robertrico/dino-homebrew/docs/images/DINO_09_10_2026_1.jpeg

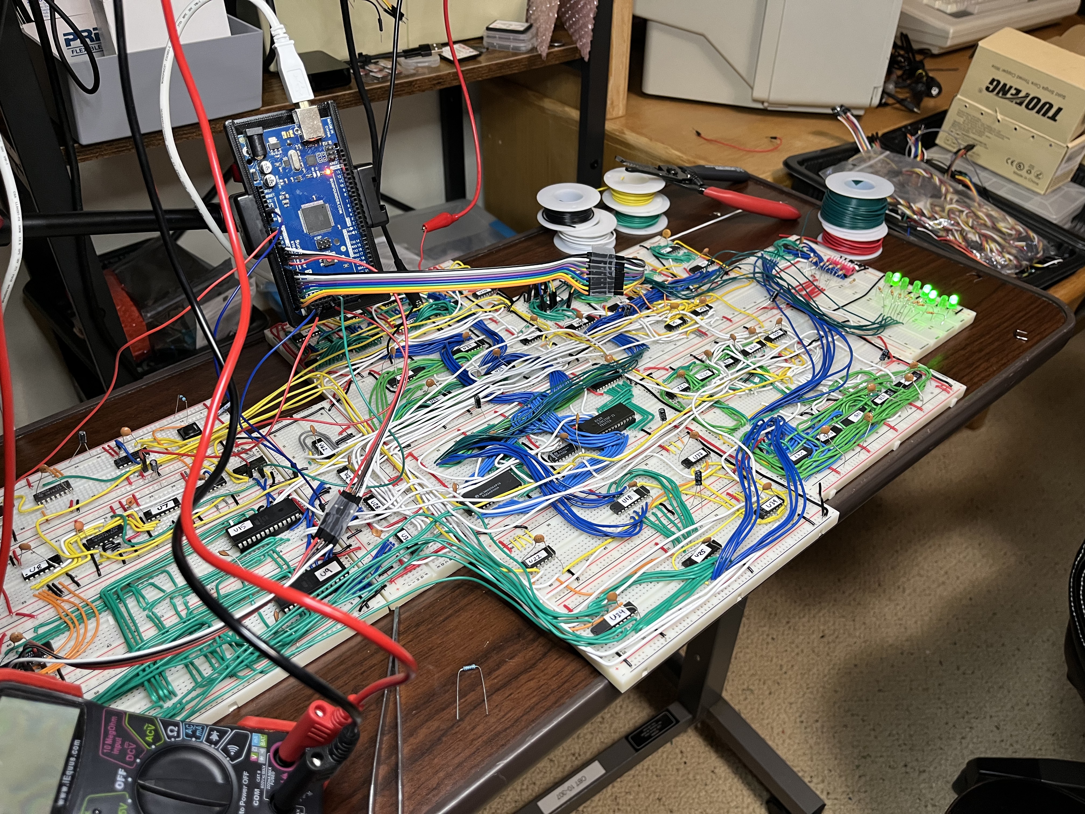
docs/images/DINO_09_10_2026_1.jpeg
