robertrico/dino-homebrew/asm/ram/bigxfer.asm

; bigxfer.asm -- the serial settle test. RAM-resident: loaded, not burned.
; 2026-09-29: RETURNS (5/5, retlda 40/40) with the T-state-0 write gate in copper
;   (U62 g4 + U56 3->4, .git/sdd/RAM_RET_FETCH.md). The results below are PRE-GATE.
;   load+run: make go-bigxfer        (asm/ram/bigxfer.asm -> RAM via L, then G)
;   soak:     python3 docs/notes/bigxfer_host.py --runs 5
;   check:    python3 docs/notes/test_bigxfer.py
;
; 2026-09-08, Rico: the fault is mechanical -- shifting the table changes
; it -- and 301 bytes loads consistently. Before the bench time goes to the
; PCB, one witness: a LARGE transfer, both directions, several times. This
; is it. About 2.2K goes IN through L (4400 characters, each echoed and
; checked, the sum witnessed by the monitor), then G runs it and it streams
; ITSELF back OUT: every byte from 0x8100 to its own end as two hex digits,
; 32 bytes a line, then one line
;
;     S hhll X xx
;
; with the 16-bit sum and the 8-bit xor of everything it read. The host
; compares the stream byte for byte against what it assembled, and the sums
; against its own. A wire that has settled passes this several times in a
; row; a wire that has not names the byte where it slipped.
;
; OB shows the pointer's HIGH byte while it streams, 0x81 up to 0x89: a
; stall names its page.
;
; The data is 2048 bytes from a seeded generator -- no structure, every
; value, so a stuck bit or a shifted nibble cannot hide. Code first, table
; after; the walk covers both, so the code bytes are read as data too.
;
; RAM: cells at 0x8000-0x800F. The monitor's 0x80E0-0x80FF is never touched.
; REGISTER DISCIPLINE, monitor.asm's rules: B is destroyed by every
; immediate-ALU op and by INR/DCR/SHL/NOT, so B is loaded right before each
; use; nothing lives in C across a CALL (RET's scratch).
; FIRST-OF-ITS-KIND: a RAM program reading its own code bytes as data
; through LDAX (life read only its tables); a 16-bit pointer walked across
; page boundaries 0x81..0x89 (every image so far kept its pointer in one
; page); JNC on ADD's carry to ripple a 16-bit sum (JNC has only ever
; followed SUB/CPI). Everything else is monitor idiom.
;
; 2026-10-06: the sum ripples with ACI 0 now, not JNC/INR -- NEEDS THE
; CARRY MICROCODE (U9 0x4102 U15 0x9BC4 U23 0x8A40). First RAM program on
; ACI; first ACI whose carry crossed LDA/STA rows to reach it.

PUTHEX:   .equ  0x02C4          ; monitor.asm, `make listing-monitor`
PUTC:     .equ  0x0345
CRLF:     .equ  0x036B

PTRL:     .equ  0x8000          ; walk pointer
PTRH:     .equ  0x8001
CUR:      .equ  0x8002          ; the byte just read
S16L:     .equ  0x8003          ; 16-bit sum
S16H:     .equ  0x8004
XR:       .equ  0x8005          ; 8-bit xor
COL:      .equ  0x8006          ; bytes on this line

          .org  0x8100

start:    MVI   PTRL, <start
          MVI   PTRH, >start
          CLR
          STA   S16L
          STA   S16H
          STA   XR
          STA   COL

loop:     LDB   PTRH
          LDC   PTRL
          LDAX                  ; A = [PTR]
          STA   CUR
          LDB   PTRH
          MOVAB
          OUT                   ; progress: the page on OB

          LDB   CUR             ; S16 += CUR, carry into the high byte
          LDA   S16L
          ADD
          STA   S16L
          LDA   S16H            ; LDA/STA hold the flags: ADD's carry
          ACI   0x00            ;   is still C here
          STA   S16H
          LDB   CUR             ; XR ^= CUR
          LDA   XR
          XOR
          STA   XR

          LDA   CUR             ; print it
          CALL  PUTHEX
          LDA   COL             ; 32 to a line
          INR
          STA   COL
          CPI   32
          JNZ   no_crlf
          CALL  CRLF
          CLR
          STA   COL
no_crlf:  LDA   PTRL            ; PTR += 1
          INR
          STA   PTRL
          JNZ   check
          LDA   PTRH
          INR
          STA   PTRH
check:    LDA   PTRL            ; until PTR == end
          CPI   <end
          JNZ   loop
          LDA   PTRH
          CPI   >end
          JNZ   loop

          LDA   COL             ; end the last line if it is open
          CPI   0
          JNZ   tail_crlf
          JMP   report
tail_crlf: CALL CRLF
report:   LDAI  'S'
          CALL  PUTC
          LDAI  ' '
          CALL  PUTC
          LDA   S16H
          CALL  PUTHEX
          LDA   S16L
          CALL  PUTHEX
          LDAI  ' '
          CALL  PUTC
          LDAI  'X'
          CALL  PUTC
          LDAI  ' '
          CALL  PUTC
          LDA   XR
          CALL  PUTHEX
          CALL  CRLF
          RET

; ---- the data: 2048 bytes, random.Random(0x0D1A0), regenerate with
; python3 -c "import random;r=random.Random(0x0D1A0);print(...)"
table:
          .db   0xC6, 0xA5, 0x89, 0x42, 0x63, 0x2E, 0x91, 0x6A, 0x98, 0xDD, 0x0A, 0x0E, 0xE5, 0x60, 0xDA, 0xA2
          .db   0x3F, 0xBA, 0xC1, 0xAE, 0xF3, 0xE6, 0xFC, 0x8C, 0xB1, 0xD5, 0x8F, 0x1A, 0x45, 0x46, 0x24, 0xA1
          .db   0x86, 0xBD, 0xBA, 0x51, 0xC6, 0x12, 0x52, 0x82, 0xD9, 0xED, 0x7C, 0x0A, 0x41, 0x05, 0x95, 0x2B
          .db   0xEB, 0xE7, 0xE5, 0x90, 0xF5, 0x7F, 0xE3, 0xA2, 0x23, 0xF5, 0x74, 0xDE, 0xF0, 0xC6, 0xCB, 0x08
          .db   0x19, 0xEB, 0xFE, 0x38, 0xCA, 0x19, 0x66, 0xC2, 0x02, 0xBE, 0xC4, 0x11, 0x0B, 0x94, 0xD9, 0xB2
          .db   0x2C, 0xF2, 0x97, 0xB5, 0x1C, 0xFF, 0xB0, 0x68, 0x16, 0x2F, 0x60, 0x61, 0x89, 0x59, 0xA7, 0x88
          .db   0xCE, 0xFB, 0x7B, 0xA7, 0xC5, 0x41, 0x51, 0xF1, 0x7D, 0x91, 0xAD, 0x83, 0x56, 0x4C, 0x8F, 0x3C
          .db   0xDF, 0xB4, 0x1A, 0x03, 0xC7, 0x4C, 0xCF, 0xF4, 0xBB, 0xA3, 0xEB, 0x55, 0xEE, 0xC8, 0x48, 0xB1
          .db   0x12, 0xB5, 0x9B, 0x51, 0x0B, 0xF9, 0x81, 0x4C, 0x28, 0xE8, 0x32, 0x85, 0x75, 0x05, 0x2A, 0xF0
          .db   0x5D, 0x03, 0x81, 0xD1, 0x6F, 0x68, 0xA7, 0xE8, 0x5D, 0x31, 0xB3, 0xF5, 0xEF, 0xC5, 0x6F, 0x8A
          .db   0x49, 0x15, 0x27, 0x9F, 0x3A, 0xCA, 0x32, 0x82, 0x6A, 0xDD, 0x6B, 0xCF, 0x0A, 0x72, 0x56, 0x4A
          .db   0xCE, 0x6F, 0x52, 0x78, 0xDD, 0x01, 0xA0, 0x11, 0xD0, 0x3B, 0xA5, 0x92, 0xD2, 0x59, 0xA6, 0x74
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
          .db   0xCD, 0xCD, 0xDB, 0x6A, 0xD6, 0x27, 0xED, 0x22, 0x6D, 0xD6, 0xBD, 0x80, 0x3E, 0x08, 0xC5, 0xFE
          .db   0x84, 0x0C, 0x22, 0xA4, 0x4E, 0xCB, 0x27, 0x4A, 0xBB, 0x31, 0x7B, 0x2E, 0x1E, 0x53, 0x30, 0x98
end:
