robertrico/dino-homebrew/docs/notes/microcode_gen.py

#!/usr/bin/env python3
"""DINO microcode ROM image generator.

Symbolic instruction table (dino_session_state.md "Instruction microwords")
-> U9.bin (word[7:0] = CW0-7) + U15.bin (word[15:8] = CW8-15), the diag
image pair, printed per-chip CRC16s, and the rig's expect header
(tests/dino_bringup/src/microcode_expect.h) so rig and ROM can never
disagree.

Address = {IR[7:0], T[3:0]} = opcode*16 + T. 4096 rows; A12 is grounded on
the board, so each 8K AT28C64B carries the image twice (mirrored halves).

Hard rules (session state, decision item 3 + HALT rule change 2026-07-14):
  - ALL 4096 rows programmed; unused rows = SAFE-FILL 0x1000 (END).
  - T0 of ALL 256 opcodes = universal fetch 0x600E.
  - HALT word = 0x8000, bit15 only, NO END bit.

Diag image (test spec "ROM images"): word = own 12-bit address in [11:0],
INVERTED top address nibble in [15:12] — catches stuck-high data lines.

Builder asserts implement the list in dino_design_notes.md ("Builder
assert list") — the POLICY layer of the four-layer defense.

Run: python3 microcode_gen.py            (writes roms/ + expect header)
Test: python3 test_microcode_gen.py
"""
import os, sys

HERE = os.path.dirname(os.path.abspath(__file__))
ROMS = os.path.normpath(os.path.join(HERE, "..", "..", "roms"))
HDR = os.path.normpath(os.path.join(
    HERE, "..", "..", "tests", "dino_bringup", "src", "microcode_expect.h"))

# ---- control word bit map (session state, v0.0.3, COMPLETE) ------------
HALT_BIT = 1 << 15          # raw tap, active high
MUX_PC = 1 << 14            # PC_MAR_MUX: PC=1, MAR=0
PC_UP = 1 << 13             # raw tap
END = 1 << 12               # raw tap

SA = {"CLR": 0b000, "BSUB": 0b001, "SUB": 0b010, "ADD": 0b011,
      "XOR": 0b100, "OR": 0b101, "AND": 0b110, "SET": 0b111}  # [11:9]

# U29's O5 and O7 were the last two free MISC codes; the stack spends both.
# O0 is the NONE slot and can never be reclaimed, so MISC IS NOW FULL -- the
# next code needs ~{MISC_BANK} wired plus a second '138, or step 1's I/O
# decode retiring REG_OUT_LOAD to free O6.
MISC = {"NONE": 0b000, "PC_CLEAR": 0b001, "PC_LOAD": 0b010, "COND": 0b011,
        "MDR_OUT": 0b100, "SP_UP": 0b101, "REG_OUT_LOAD": 0b110,
        "SP_DOWN": 0b111}                                     # [8:6] U29

# SRC/DST codes 0-7 are BANK 0 (U28/U30, unchanged since the ROMs were first
# burned). Codes 8-15 are BANK 1 (U70/U71), reached by driving the matching
# bank bit LOW. The low three bits are the SAME CW3-CW5 / CW0-CW2 the old
# decoder sees; only the enable moves. That is what makes widening additive:
# every burned row stays valid and nothing re-encodes.
SRC = {"NONE": 0b000, "ROM": 0b001, "RAM": 0b010, "REG_A": 0b011,
       "REG_B": 0b100, "REG_C": 0b101, "ALU": 0b110, "SW": 0b111,  # [5:3] U28
       # bank 1 (U70). Code 8 MUST be a real source, never a NONE slot:
       # SRC_ACTIVE is U28.O0 and floats HIGH whenever U28 is disabled, so
       # every bank-1 code already reads "a source is active" -- which is
       # what turns the U25 bridge on so the byte reaches W. A bank-1 NONE
       # would let MDR quietly supply W with nothing driving it.
       "SP_LO": 8, "SP_HI": 9, "PC_LO": 10, "PC_HI": 11,
       # INTERRUPTS, 2026-09-25 (PROPOSAL_INT C6). U70 O4/O5, pins 11/10,
       # NC until the INT hardware lands -- decoder-inert on today's copper.
       # KONST is the '244 holding K (the injected opcode, and both vector
       # bytes); FLAGS is the '245 putting FLAG_C/Z/V/N on MDR0-3, zeros
       # above. Both are bank 1, so both land on MDR, as the rule requires.
       "KONST": 12, "FLAGS": 13}

DST = {"NONE": 0b000, "REG_A": 0b001, "REG_B": 0b010, "REG_C": 0b011,
       "MAR_LO": 0b100, "MAR_HI": 0b101, "IR": 0b110, "RAM": 0b111,  # [2:0] U30
       # bank 1 (U71). These drive the '169s' ~PE, a SYNCHRONOUS load enable
       # -- which is why the stack needs no SP_LOAD misc code and why MISC
       # got away with the two slots it had left.
       "SP_LO": 8, "SP_HI": 9,
       # INTERRUPTS, 2026-09-25. U71 O2-O4, pins 13/12/11, NC today.
       # FLAGS drives the POPF '157 in front of U49 D0-3; IE_SET / IE_CLR
       # are the interrupt-enable flip-flop's set and clear.
       "FLAGS": 10, "IE_SET": 11, "IE_CLR": 12}

# ---- the third EEPROM, CW16-23 (U23) -----------------------------------
# Every bit is ACTIVE LOW so that 0xFF -- an erased AT28C64B -- is today's
# machine. Same reasoning that made HALT=0xFF: the safe state has to be the
# blank state, or an unburned ROM rants instead of idling.
CIN_SEL_N = 1 << 16     # 0 = ALU_CIN follows FLAG_C (ADC/SBB); 1 = opcode path
SRC_BANK_N = 1 << 17    # 0 = SRC bank 1 (U70); 1 = bank 0 (U28)
DST_BANK_N = 1 << 18    # 0 = DST bank 1 (U71); 1 = bank 0 (U30)
MISC_BANK_N = 1 << 19   # 0 = MISC bank 1; 1 = bank 0.  UNWIRED, in reserve
ADDR_SEL1_N = 1 << 20   # with CW14 as ADDR_SEL0.       UNWIRED, in reserve
FLAG_SEL0 = 1 << 21     # '153 4:1 select, bit 0  \  UNWIRED, in reserve
FLAG_SEL1 = 1 << 22     # '153 4:1 select, bit 1   >  sel 00=C 01=Z 10=V 11=N
FLAG_POL = 1 << 23      # '86 polarity           /   taken = flag XOR pol

# Every third-ROM bit set = the inert word. word() starts here and CLEARS
# bits, so a field nobody names is automatically safe.
INERT_THIRD = 0xFF << 16

FLAG_SEL = {"C": 0b00, "Z": 0b01, "V": 0b10, "N": 0b11}


class BuildError(Exception):
    """Raised by word()/check_word()/check_table(). Defined here rather than
    with the other policy code below because word() itself now refuses two
    encodings -- see the two numbered refusals in its cond branch."""


def _sa_bits(code):
    """Pack a '382 function code into CW9..CW11 BIT-REVERSED.

    The schematic labels CW9=SA2, CW10=SA1, CW11=SA0, and wires SA0 -> S0,
    SA1 -> S1, SA2 -> S2. So CW9 carries the '382's select MSB and CW11 its
    LSB. Packing the code LSB-first at CW9 therefore delivers it REVERSED:
    ADD (011) arrived as 110 = AND, which is precisely what the bench measured
    — 5 AND 3 = 1, 0x39 AND 0 = 0, 0 AND 0x39 = 0, three independent images
    all matching (2026-08-02).

    This survived every earlier test because reversing a field is INVISIBLE
    unless something computes with it: block1 checked ROM -> pin and found them
    self-consistent, and alu.ops drove SA from the rig, never using the
    microcode's encoding at all. test_microcode_gen.py now cross-checks this
    against the NETLIST so it cannot come back.
    """
    return ((code & 1) << 2) | (code & 2) | ((code >> 2) & 1)


def word(mux_pc=False, pc_up=False, end=False, halt=False,
         sa=None, misc="NONE", src="NONE", dst="NONE",
         cin_from_flag_c=False, cond=None):
    """One 24-bit control word.

    `src`/`dst` name a code in EITHER bank -- the bank bit is derived from
    the code, never passed by hand, so a caller cannot select `SP_LO` and
    forget to switch banks.

    `cond=(flag, pol)` encodes the '153/'86 branch glue: `flag` is one of
    C/Z/V/N and `pol` is 0 or 1, with `taken = flag XOR pol`. The hardware
    does not exist yet; the field is burned now so it never needs a reburn.
    """
    w = INERT_THIRD
    if halt: w |= HALT_BIT
    if mux_pc: w |= MUX_PC
    if pc_up: w |= PC_UP
    if end: w |= END
    if sa is not None: w |= _sa_bits(SA[sa]) << 9

    m, s, d = MISC[misc], SRC[src], DST[dst]
    w |= (m & 7) << 6
    w |= (s & 7) << 3
    w |= (d & 7)
    # Codes 8-15 live in bank 1, selected by driving the bank bit LOW.
    if s >= 8: w &= ~SRC_BANK_N
    if d >= 8: w &= ~DST_BANK_N
    if m >= 8: w &= ~MISC_BANK_N

    if cin_from_flag_c: w &= ~CIN_SEL_N
    if cond is not None:
        flag, pol = cond
        sel = FLAG_SEL[flag]
        # BOTH refusals below are for faults that ENCODE CLEANLY, BURN, and
        # then branch on the wrong thing with nothing to say so. Same class
        # as the bit-reversed SA field: invisible unless something computes.
        #
        # 1. U77 is a 2:1 on CW21 ALONE. CW22 is a no-connect. V (0b10) and
        #    N (0b11) both have bit 0 CLEAR, so encoding either drives CW21
        #    LOW and hands U62.3 FLAG_C. Refuse until CW22 is landed -- and
        #    when it is, DELETE this branch, do not weaken it.
        if sel & 2:
            raise BuildError(
                f"cond flag {flag!r} needs CW22, which is a NO-CONNECT: U77 "
                f"is a 2:1 on CW21 alone, so {flag} would select FLAG_C")
        # 2. word()'s contract says taken = flag XOR pol. The BUILT gate is
        #    COND_TAKEN = NOR(~{COND}, flag) = flag XOR 1, and there is no
        #    '86 anywhere in this machine. Encoder and copper agree at
        #    pol=1 only; pol=0 clears CW23 and inverts every branch the day
        #    polarity lands.
        if not pol:
            raise BuildError(
                "cond pol=0 needs FLAG_POL/CW23 and a '86; the built gate is "
                "COND_TAKEN = NOR(~{COND}, flag), which is pol=1")
        if not (sel & 1): w &= ~FLAG_SEL0
        if not (sel & 2): w &= ~FLAG_SEL1
        if not pol: w &= ~FLAG_POL
    return w


FETCH = word(mux_pc=True, pc_up=True, src="ROM", dst="IR")   # 0x600E
FILL = word(end=True)                                        # 0x1000, END

# A SETTLING STATE. No source, no destination, no strobe -- electrically
# identical to SAFE_FILL minus its END, and SAFE_FILL occupies 4000 rows of
# the image already, so this drives nothing new.
#
# WHY IT EXISTS, 2026-08-27. An instruction that loads an ALU operand and
# reads the ALU in the VERY NEXT state gives the '382 pair no settling time:
# the operand latch closes on the CLK edge that ends one state and the result
# must be valid inside the next. Every other instruction in the machine loads
# its operand in a PREVIOUS instruction and gets a whole fetch state for free.
#
# At 500kHz all 147 subtests of PROG_isa pass. At 1.024MHz the same image
# returns varying subtest numbers from identical resets. Subtract runs out of
# margin first, because a '382 complements B before the adder starts -- ADI
# passed in the same run that SUI failed.
#
# One state each, byte lengths unchanged, no package.
SETTLE = word()                                              # 0xFF0000


# ---- opcode assignments -------------------------------------------------
# PROPOSED TABLE (2026-07-16). Only LDAI=0x11 is documented (addressing
# example in dino_session_state.md) — everything else is a fresh assignment:
# high nibble = family (0=ctl, 1=imm loads, 2=memory, 3=flow, 4=ALU, 5=io),
# HALT=0xFF so an ERASED program EEPROM (all 0xFF) halts instead of raving.
# Renumbering = edit here, rerun, reburn; the rig follows via the header.
OPCODES = {
    "NOP": 0x00,
    "LDAI": 0x11, "LDBI": 0x12, "LDCI": 0x13,
    "LDA": 0x21, "STA": 0x22,
    "JMP": 0x31, "JNZ": 0x32,
    "ADD": 0x41, "SUB": 0x42, "AND": 0x43, "OR": 0x44,
    "XOR": 0x45, "CLR": 0x46, "SET": 0x47, "BSUB": 0x48,
    # 0x52 WAS `IN`, RETIRED 2026-08-27 (Rico), at the burn SECTION 5 named.
    # It went in two stages and they are different KINDS of retirement:
    # phase E retired it in COPPER (U28.7 unlanded, ~{SW_OUT} deleted, SW1
    # answers at an ADDRESS as card zero and LDA replaces it) but kept the
    # row, because phase E burned no microcode ROM and deleting a row would
    # have cost three ROMs for nothing. Phase F writes all three anyway.
    # Executing IN on today's copper reads an UNDEFINED byte, not the park:
    # src=SW asserts SRC_ACTIVE so U25 is enabled, but SW asserts neither
    # ~{ROM_OUT} nor ~{RAM_OUT}, so READS_IDLE stays high and U25 drives W
    # from a floating MDR. 0x52 is free. Nothing claims it.
    "OUT": 0x51,
    # --- the stack, 2026-08-10 ------------------------------------------
    # LXISP joins the immediate-load family; CALL/RET join flow; PUSH/POP
    # open a 0x6x stack family. All five are reachable only because the
    # third EEPROM widened SRC and DST.
    "LXISP": 0x14,
    "CALL": 0x33, "RET": 0x34,
    "PUSHA": 0x61, "POPA": 0x62, "PUSHB": 0x63, "POPB": 0x64,
    "HALT": 0xFF,

    # --- PHASE F, 2026-08-27: forty free instructions plus JNC ----------
    # SECTION 6 of .git/sdd/PHASE_F.md is the collision-free map and this is
    # it, verbatim. Family 9 (SHR/MOV A,FLAGS/ADC/SBB) is NOT here: those
    # need packages that are not in sockets, and family 9 means "does not
    # exist until a package lands".
    #
    # ONE BURN COVERS ALL OF THEM. A new opcode writes rows in every byte of
    # the 24-bit word, so three ROMs is the cost of adding one instruction
    # AND the cost of adding forty-one. Adding MOV A,C alone would have cost
    # exactly what this costs.
    "RST": 0x01,
    "LDB": 0x23, "LDC": 0x24, "STB": 0x25, "STC": 0x26,
    "LDAS": 0x27, "STAS": 0x28,
    "JMPX": 0x35, "JMPSP": 0x36,
    "JNC": 0x37,                    # the ONLY one that needs U77
    "CMP": 0x49, "CMPB": 0x4A, "TST": 0x4B,
    "SHL": 0x4C, "INR": 0x4D, "DCR": 0x4E, "NOT": 0x4F,
    "PUSHC": 0x65, "POPC": 0x66,
    "INXSP": 0x67, "DCXSP": 0x68, "SPHL": 0x69, "HLSP": 0x6A,
    "LDAX": 0x71, "STAX": 0x72, "LDBX": 0x73, "STBX": 0x74,
    "LDCX": 0x75, "STCX": 0x76,
    # MOV dst,src -- the mnemonic reads MOVAB = "MOV A,B" = A <- B. The
    # names carry no comma because they are dict keys and assembler steps.
    "MOVAB": 0x81, "MOVAC": 0x82, "MOVBA": 0x83,
    "MOVBC": 0x84, "MOVCA": 0x85, "MOVCB": 0x86,
    "MOVASPL": 0x87, "MOVASPH": 0x88, "MOVSPLA": 0x89, "MOVSPHA": 0x8A,
    "MOVAPCL": 0x8B, "MOVAPCH": 0x8C,
}

# operand-fetch prefix shared by every MAR-consuming instruction:
# T1 -> MAR_LO, T2 -> MAR_HI (both fetch a byte, PC++)
_MARFILL = [word(mux_pc=True, pc_up=True, src="ROM", dst="MAR_LO"),   # 0x600C
            word(mux_pc=True, pc_up=True, src="ROM", dst="MAR_HI")]   # 0x600D


def _alu(op):
    return [word(end=True, sa=op, src="ALU", dst="REG_A")]


# SP -> MAR, the two-state prefix every stack access starts with. SP is a
# number, not an address driver (Route B), so MAR does the pointing.
_SP_TO_MAR = [word(src="SP_LO", dst="MAR_LO"),
              word(src="SP_HI", dst="MAR_HI")]


# B:C -> MAR, the two-state prefix every indexed access starts with. C is
# the LOW half: MAR_LO is loaded first and from C, without exception. A
# swapped pair is an off-by-256 and a round trip through the same pointer
# cannot see it.
_BC_TO_MAR = [word(src="REG_C", dst="MAR_LO"),
              word(src="REG_B", dst="MAR_HI")]


def _PUSH_BYTE(src):
    """Store one byte at [SP], then decrement. Empty-descending."""
    return _SP_TO_MAR + [word(src=src, dst="RAM"), word(misc="SP_DOWN")]


def _PUSH(reg):
    states = _PUSH_BYTE(reg)
    return states[:-1] + [word(misc="SP_DOWN", end=True)]


def _POP(reg):
    """Increment first, THEN load -- the mirror of PUSH's store-then-drop."""
    return ([word(misc="SP_UP")] + _SP_TO_MAR
            + [word(end=True, src="RAM", dst=reg)])


# instruction -> (byte length, [T1, T2, ...]); T0 is implicit FETCH
INSTRUCTIONS = {
    "NOP": (1, [word(end=True)]),
    "LDAI": (2, [word(mux_pc=True, pc_up=True, end=True, src="ROM", dst="REG_A")]),
    "LDBI": (2, [word(mux_pc=True, pc_up=True, end=True, src="ROM", dst="REG_B")]),
    "LDCI": (2, [word(mux_pc=True, pc_up=True, end=True, src="ROM", dst="REG_C")]),
    "LDA": (3, _MARFILL + [word(end=True, src="RAM", dst="REG_A")]),
    "STA": (3, _MARFILL + [word(end=True, src="REG_A", dst="RAM")]),
    "JMP": (3, _MARFILL + [word(end=True, misc="PC_LOAD")]),
    # JNZ NAMES ITS FLAG NOW, and that is the CW22 cure, not cosmetics.
    # A bare misc="COND" leaves the third ROM's default word -- CW21=1,
    # CW22=1, CW23=1 -- and under FLAG_SEL {CW22,CW21} = 0b11 is `N`, not
    # `Z`. It behaved as Z only because FLAG_Z was hardwired to U62.3. Land a
    # 4:1 on {CW22,CW21} later without a reburn and EVERY JNZ IN THE MACHINE
    # BECOMES JNN. cond=("Z",1) drives CW22 low now, so the second mux stage
    # is itself inert when it lands. pol=1 because the built gate is
    # COND_TAKEN = NOR(~{COND}, flag) and there is no '86 in this machine.
    "JNZ": (3, _MARFILL + [word(end=True, misc="COND", cond=("Z", 1))]),
    "ADD": (1, _alu("ADD")), "SUB": (1, _alu("SUB")),
    "AND": (1, _alu("AND")), "OR": (1, _alu("OR")),
    "XOR": (1, _alu("XOR")), "CLR": (1, _alu("CLR")),
    "SET": (1, _alu("SET")), "BSUB": (1, _alu("BSUB")),
    "OUT": (1, [word(end=True, misc="REG_OUT_LOAD", src="REG_A")]),
    # IN's ROW IS GONE, 2026-08-27. See OPCODES above for why, and
    # test_microcode_gen.test_IN_is_retired_from_the_isa for the guard that
    # stops it coming back. SW1 is read with LDA now -- it is memory.

    # --- the stack ------------------------------------------------------
    #
    # CONVENTION: empty-descending. SP points at the next FREE slot, PUSH
    # stores then decrements, POP increments then loads. A '169 has no
    # clear, so SP is RANDOM at power-up and every program must run LXISP
    # before touching the stack -- "machine works, then randomly doesn't"
    # traced to an unset SP is a miserable afternoon.
    #
    # SP never reaches the address bus directly (Route B). It is just a
    # number; MAR is the thing that points, so every stack access copies
    # SP into MAR first. That costs two T-states per access and buys back
    # the structural guarantee that M has exactly one driver pair.

    # LXISP addr -- the initialiser every program needs first.
    "LXISP": (3, [word(mux_pc=True, pc_up=True, src="ROM", dst="SP_LO"),
                  word(mux_pc=True, pc_up=True, end=True,
                       src="ROM", dst="SP_HI")]),

    "PUSHA": (1, _PUSH("REG_A")), "PUSHB": (1, _PUSH("REG_B")),
    "POPA": (1, _POP("REG_A")), "POPB": (1, _POP("REG_B")),

    # CALL addr -- push the return address, THEN fetch the target.
    #
    # The order is forced: CALL needs two 16-bit values alive at once (the
    # return address and the target) and MAR is the only 16-bit holder, so
    # the push has to finish before MAR is reused to fetch the target.
    #
    # THE PRICE, and it is a real one: what gets pushed is the address of
    # CALL's OPERAND BYTES, not the instruction after them. RET therefore
    # ends with two bare PC_UPs to step over them. Written once here,
    # host-tested, cannot drift.
    "CALL": (3, _PUSH_BYTE("PC_HI") + _PUSH_BYTE("PC_LO") + [
        word(mux_pc=True, pc_up=True, src="ROM", dst="MAR_LO"),
        word(mux_pc=True, pc_up=True, src="ROM", dst="MAR_HI"),
        word(end=True, misc="PC_LOAD"),
    ]),

    # RET -- pop two bytes back into MAR, load the PC from it, then step
    # over the operand bytes per the CALL convention above.
    #
    # The LO byte has to be parked somewhere while MAR is re-pointed at the
    # HI byte's slot, and C is the machine's only free register. That is
    # the whole reason RET clobbers C, and it is why C stays unavailable to
    # user code until a real scratch exists.
    "RET": (1, [
        word(misc="SP_UP"),
        word(src="SP_LO", dst="MAR_LO"),
        word(src="SP_HI", dst="MAR_HI"),
        word(src="RAM", dst="REG_C"),        # return LO parked in C
        word(misc="SP_UP"),
        word(src="SP_LO", dst="MAR_LO"),
        word(src="SP_HI", dst="MAR_HI"),
        # Return HI onto the bus with NO destination -- MDR shadows every W
        # transfer for free (U22 gate2: ~{MDR_EN} = NOR(SRC_ACTIVE, MDR_OUT),
        # so the U25 bridge is on whenever ANY source drives), and LE_MDR =
        # NAND(~{RAM_LOAD}, READS_IDLE) latches that byte the moment the read
        # ends. That gives RET the SECOND scratch it needs without a second
        # register, and it is why src=RAM dst=MAR_HI is NOT used here -- see
        # check_word's RAM-writes-MAR rule.
        word(src="RAM"),
        # REPLAY IMMEDIATELY -- the very next state, before anything else
        # drives MDR. U18's LE_MDR falls as ~{RAM_OUT} deasserts at the
        # T-state boundary, and if another source is turning ON across that
        # same boundary the latch can capture THAT byte instead. Found on the
        # gate model 2026-08-10: with one intervening REG_C -> MAR_LO state,
        # U18 latched C (0x0C) and RET loaded PC = 0x0C0C instead of 0x000C.
        # Reasoning said the park was safe; the model disagreed.
        word(misc="MDR_OUT", dst="MAR_HI"),  # parked HI out of MDR
        word(src="REG_C", dst="MAR_LO"),     # parked LO out of C
        word(misc="PC_LOAD"),                # PC <- M <- MAR
        word(pc_up=True),                    # step over operand byte 1
        word(pc_up=True, end=True),          # step over operand byte 2
    ]),

    "HALT": (1, [word(halt=True)]),

    # ====================================================================
    # PHASE F, 2026-08-27 -- forty instructions that cost no wire, plus JNC
    # which costs exactly one package (U77, the '157 flag mux).
    #
    # Every code below was ALREADY LANDED and, with five exceptions noted in
    # CLAUDE.md, already bench-proven. Nothing here decodes to a pin that has
    # never been driven; what was missing was rows, not copper.
    # ====================================================================

    # ---- JNC: the one instruction in this block that needs hardware -----
    # Identical to JNZ but for CW21. COND_TAKEN = NOR(~{COND}, flag), so the
    # machine has exactly ONE branch polarity -- "taken if the selected flag
    # is ZERO" -- and U77 changes which flag, never the sense.
    #
    # The '382 pair's CN+4 is a NOT-borrow on the subtract codes, so
    # FLAG_C = 0 means A < B unsigned. JNC is therefore an unsigned magnitude
    # branch, and with CMP it asks "less than" without destroying A. The free
    # polarity is also the RIGHT one for multi-byte arithmetic: ADD; JNC
    # skip; <carry into the high byte> is the carry-propagate idiom exactly.
    # That is luck, not design, and it is why FLAG_POL can stay unlanded.
    "JNC": (3, _MARFILL + [word(end=True, misc="COND", cond=("C", 1))]),

    # ---- register moves -------------------------------------------------
    # SRC 3/4/5 = U28.O3/O4/O5, DST 1/2/3 = U30.O1/O2/O3. U28.O5 and U30.O3
    # were first driven by RET (T10 and T4) on 2026-08-24; the rest have run
    # since the machine booted.
    #
    # MOV A,C is the row that RETIRES THE LDCI GAP. LDCI and NOP are the only
    # two instructions that have never executed, and LDCI is unreachable BY
    # DESIGN because C is RET's return-address scratch and nothing can read
    # it back. One row closes it. That gap was always MICROCODE-SOFT.
    "MOVAB": (1, [word(end=True, src="REG_B", dst="REG_A")]),
    "MOVAC": (1, [word(end=True, src="REG_C", dst="REG_A")]),
    "MOVBA": (1, [word(end=True, src="REG_A", dst="REG_B")]),
    "MOVBC": (1, [word(end=True, src="REG_C", dst="REG_B")]),
    "MOVCA": (1, [word(end=True, src="REG_A", dst="REG_C")]),
    "MOVCB": (1, [word(end=True, src="REG_B", dst="REG_C")]),

    # ---- SP and PC readback ---------------------------------------------
    # SRC 8/9 = U70.O0/O1 (bench-proven by PROG_sp), SRC 10/11 = U70.O2/O3
    # (bench-proven by CALL T3/T7), DST 8/9 = U71.O0/O1 (bench-proven by
    # LXISP). Registers sit on MDR0-7 and so does the SP readback pair, so
    # these are plain one-row transfers with no new decoder output.
    #
    # MOV A,SPL / MOV SPL,A are what make SP usable as a SECOND INDEX
    # REGISTER in a leaf routine: it can be saved and restored. A routine
    # that also uses CALL or PUSH cannot do this, and that is a real
    # constraint, not a footnote.
    "MOVASPL": (1, [word(end=True, src="SP_LO", dst="REG_A")]),
    "MOVASPH": (1, [word(end=True, src="SP_HI", dst="REG_A")]),
    "MOVSPLA": (1, [word(end=True, src="REG_A", dst="SP_LO")]),
    "MOVSPHA": (1, [word(end=True, src="REG_A", dst="SP_HI")]),
    "MOVAPCL": (1, [word(end=True, src="PC_LO", dst="REG_A")]),
    "MOVAPCH": (1, [word(end=True, src="PC_HI", dst="REG_A")]),

    # B:C <-> SP, the union of the two rows above. C is the LOW half
    # throughout this document and this file -- see the pointer group.
    "SPHL": (1, [word(src="REG_C", dst="SP_LO"),
                 word(end=True, src="REG_B", dst="SP_HI")]),
    "HLSP": (1, [word(src="SP_LO", dst="REG_C"),
                 word(end=True, src="SP_HI", dst="REG_B")]),

    # ---- compares: an ALU op with NO destination -------------------------
    # U49 (the '273 flag latch) HAS NO CLOCK ENABLE -- it re-clocks every
    # T-state -- and U48's select is ~{ALU_OUT}. So the flags update on any
    # row that sources the ALU, whether or not anything latches the result.
    # DST 0 is U30.O0, the NONE slot, a no-connect by design.
    #
    # CMP is what makes JNC worth having: SUB then JNZ can only ask "equal or
    # not", and CMP + JNC asks "less than" without destroying A.
    "CMP": (1, [word(end=True, sa="SUB", src="ALU", dst="NONE")]),
    "CMPB": (1, [word(end=True, sa="BSUB", src="ALU", dst="NONE")]),
    "TST": (1, [word(end=True, sa="OR", src="ALU", dst="NONE")]),

    # ---- control ---------------------------------------------------------
    # MISC 1 = U29.O1, in use since the machine booted. RST is PC_CLEAR with
    # no operand: a one-byte software reset that does NOT clear the stack,
    # the registers or OB. Say which reset you mean.
    "RST": (1, [word(end=True, misc="PC_CLEAR")]),

    # MISC 5/7 = U29.O5/O7, bench-proven by POP and PUSH. SP_UP/SP_DOWN are
    # THE ONLY 16-BIT ARITHMETIC IN THE MACHINE and they touch neither the
    # ALU nor the flags. B:C has nothing comparable -- there is no carry path
    # between the registers -- so INXSP is the incrementer a monitor walks a
    # pointer with.
    "INXSP": (1, [word(end=True, misc="SP_UP")]),
    "DCXSP": (1, [word(end=True, misc="SP_DOWN")]),

    # ---- indirect jumps --------------------------------------------------
    # MISC 2 = U29.O2, in use by JMP. One byte: the target is in B:C or SP,
    # not in the instruction stream, so there is no PC_UP past the fetch.
    "JMPX": (1, [word(src="REG_C", dst="MAR_LO"),
                 word(src="REG_B", dst="MAR_HI"),
                 word(end=True, misc="PC_LOAD")]),
    "JMPSP": (1, _SP_TO_MAR + [word(end=True, misc="PC_LOAD")]),

    # ---- B:C as an index pair -------------------------------------------
    # C IS THE LOW BYTE. MAR_LO is loaded first and from C, everywhere in
    # this file, and a swapped pair is an off-by-256 that a round trip
    # through the SAME pointer cannot see -- the PROG_sp1 lesson, which
    # reported a green machine for most of 2026-08-24 with every bank-1
    # decoder output dead. Any witness for these must read back a cell only
    # a MOVED pointer reaches, by a path that cannot inherit the fault.
    #
    # src=RAM writing MAR is the forbidden case (the address feeds back into
    # the read while the '373 is transparent); this is not it -- MAR is
    # loaded from W, off the registers, before RAM is touched at all.
    "LDAX": (1, _BC_TO_MAR + [word(end=True, src="RAM", dst="REG_A")]),
    "LDBX": (1, _BC_TO_MAR + [word(end=True, src="RAM", dst="REG_B")]),
    "LDCX": (1, _BC_TO_MAR + [word(end=True, src="RAM", dst="REG_C")]),
    "STAX": (1, _BC_TO_MAR + [word(end=True, src="REG_A", dst="RAM")]),
    "STBX": (1, _BC_TO_MAR + [word(end=True, src="REG_B", dst="RAM")]),
    "STCX": (1, _BC_TO_MAR + [word(end=True, src="REG_C", dst="RAM")]),

    # ---- SP as a pointer -------------------------------------------------
    # The prefix is PUSH's, verbatim. A routine using LDAS/STAS cannot also
    # be using the stack for calls -- named in the docs, not hidden here.
    "LDAS": (1, _SP_TO_MAR + [word(end=True, src="RAM", dst="REG_A")]),
    "STAS": (1, _SP_TO_MAR + [word(end=True, src="REG_A", dst="RAM")]),

    # ---- absolute loads/stores for B and C -------------------------------
    # _MARFILL is LDA's prefix verbatim. DST 7 = U30.O7, in use by STA.
    "LDB": (3, _MARFILL + [word(end=True, src="RAM", dst="REG_B")]),
    "LDC": (3, _MARFILL + [word(end=True, src="RAM", dst="REG_C")]),
    "STB": (3, _MARFILL + [word(end=True, src="REG_B", dst="RAM")]),
    "STC": (3, _MARFILL + [word(end=True, src="REG_C", dst="RAM")]),

    # ---- C joins the stack ----------------------------------------------
    # Identical shape to PUSHA/POPA, bench-proven by PROG_sp2. Together with
    # MOV A,C these give C a life beyond being RET's scratch -- but RET still
    # clobbers it, so a routine that calls anything must not expect C to
    # survive the call.
    "PUSHC": (1, _PUSH("REG_C")), "POPC": (1, _POP("REG_C")),

    # ---- the TMP-shadow arithmetic ---------------------------------------
    # ALL FOUR CLOBBER B. That is the price and it is stated, not buried.
    #
    # They cost TWO rows and not four because U45/U46 (the ALU's TMP_A/TMP_B
    # '373 shadows) latch on the LOAD STROBE, not the opcode:
    #     LE_TMP_B = NOR(~{REG_B_LOAD}, CLK)          U50 g2
    # so ANY row with dst=REG_B fills TMP_B and the NEXT row's ALU op sees
    # it. Same mechanism that made the retired IN work in one microword.
    #
    # SHL:  row 1 copies A into B, so row 2 computes A + A.
    # INR:  SET makes 0xFF; A - 0xFF = A + 1 (mod 256).
    # DCR:  A + 0xFF = A - 1.
    # NOT:  A XOR 0xFF.
    # INR/DCR/NOT spend row 1 on the ALU itself (sa=SET, dst=REG_B), which
    # is why their first row sources ALU where SHL's sources REG_A.
    "SHL": (1, [word(src="REG_A", dst="REG_B"), SETTLE,
                word(end=True, sa="ADD", src="ALU", dst="REG_A")]),
    "INR": (1, [word(sa="SET", src="ALU", dst="REG_B"), SETTLE,
                word(end=True, sa="SUB", src="ALU", dst="REG_A")]),
    "DCR": (1, [word(sa="SET", src="ALU", dst="REG_B"), SETTLE,
                word(end=True, sa="ADD", src="ALU", dst="REG_A")]),
    "NOT": (1, [word(sa="SET", src="ALU", dst="REG_B"), SETTLE,
                word(end=True, sa="XOR", src="ALU", dst="REG_A")]),
}


# ==========================================================================
# PHASE F+, 2026-08-27 (Rico: "max the ceiling with all legal hardware-less
# instructions"). 108 more instructions, ZERO packages, ZERO new decoder
# outputs. Every row below uses a SRC, DST and MISC code that is already
# landed in copper and, with the five exceptions CLAUDE.md names, already
# bench-proven.
#
# WHY THIS MANY EXIST AT ALL. The decoders were widened twice -- for the
# stack (bank 1, 2026-08-10) and for CALL/RET (U72/U73, phase C) -- and the
# ROWS to use the new codes were only ever written for the instructions that
# motivated the widening. Everything here was legal the day the copper
# landed and simply had no opcode.
#
# THE ENUMERATION WAS EXHAUSTIVE, NOT INSPIRED. 227 distinct legal row
# sequences exist over the landed codes; 55 were already the ISA, 172 were
# new. These are the 108 that survived curation -- see _CUT, which names
# every rejected family and why, because "we considered it and said no" is
# not recoverable from an absence.
#
# THE BINDING CONSTRAINT MOVED. It is no longer hardware, it is the 256-entry
# opcode map: all 172 would have left 18 free, and family 9 plus the CW22 and
# CW23 branch families already claim 10 of those.
#
# HIGH NIBBLE IS STILL THE FAMILY. That is what lets a byte be
# hand-disassembled at the bench, so new families take CONTIGUOUS blocks and
# spill into 0xA-0xE rather than filling whatever hole comes next. 0x9x stays
# RESERVED: family 9 means "this opcode does not exist until a package lands".
# ==========================================================================

_CUT = {
    "CLR/SET with dst=NONE":
        "computes a constant and discards it; the flags it would set are "
        "known without executing it",
    "immediate + CLR/SET":
        "CLR and SET read no operand, so the immediate byte is fetched and "
        "ignored -- CLR with a wasted byte, not an instruction",
    "SP_LO <-> SP_HI transfers":
        "no use case was named. Copying half a pointer onto its own other "
        "half is not an addressing mode",
    "PC halves -> SP halves":
        "PUSHPCL/PUSHPCH already put the PC somewhere useful and JMPSP is "
        "the reverse direction",
    "ALU result -> SP_LO/SP_HI":
        "16 opcodes for SP arithmetic that an ALU op plus MOVSPLA does in "
        "two instructions. Too rare to earn a family",
    "LD/ST of the SP halves THROUGH the SP":
        "degenerate -- the pointer loading itself from what it points at",
    "conditional branch to SP":
        "JNZ over a JMPSP is two instructions and the case is rare",
    "OUT of an ALU result through the indexed/SP prefixes":
        "OUTM/OUTMX/OUTMS already read memory to OB; an ALU result needs no "
        "address at all",
}

# name -> opcode. FROZEN AND EXPLICIT. Blocks are contiguous and each names
# its family; test_microcode_gen asserts no collision and that not one
# pre-existing opcode moved. Renumbering costs a reburn AND a reassemble of
# every program image, so this table is append-only in practice.
_OPCODES_F_PLUS = {
    # 0x1x  immediate loads -- one SP half at a time
    "LXIL": 0x15, "LXIH": 0x16,
    # 0x2x  memory: SP-relative for B and C (A got LDAS/STAS in phase F)
    "LDBS": 0x29, "STBS": 0x2A, "LDCS": 0x2B, "STCS": 0x2C,
    # 0x3x  flow: indirect branches, then the indirect loads and stores that
    #       share their five-byte operand shape
    "JZX": 0x38, "JCX": 0x39, "JMPM": 0x3A, "JZM": 0x3B, "JCM": 0x3C,
    "LDAM": 0x3D, "LDBM": 0x3E, "STAM": 0x3F,
    # 0x4x  ALU -- the last free slot in the family
    "BIT": 0x40,
    # 0x5x  I/O: OUT from any SOURCE. U44 is a '245 with its A side on
    #       MDR0-7 and ~CE = ~{REG_OUT_LOAD}, so OB latches whatever is on
    #       the bus when the strobe fires. src=REG_A was a microcode
    #       convention, never a wire.
    "OUTB": 0x52, "OUTC": 0x53, "OUTSPL": 0x54, "OUTSPH": 0x55,
    "OUTPCL": 0x56, "OUTPCH": 0x57, "OUTI": 0x58,
    "OUTM": 0x59, "OUTMX": 0x5A, "OUTMS": 0x5B,
    # 0x6x  stack: push and pop the pointers themselves
    "PUSHPCH": 0x60, "PUSHSPL": 0x6B, "POPSPL": 0x6C,
    "PUSHSPH": 0x6D, "POPSPH": 0x6E, "PUSHPCL": 0x6F,
    # 0x7x  indexed through B:C
    "MVIX": 0x77, "STADDX": 0x78, "STSUBX": 0x79, "STBSUBX": 0x7A,
    "STANDX": 0x7B, "STORX": 0x7C, "STXORX": 0x7D,
    # 0x9x  RESERVED -- hardware-gated. 0x90-0x95 went to INTERRUPTS
    #       2026-09-25 (see _OPCODES_INT). SHR (U78), MOV A,FLAGS (U79),
    #       ADC/SBB (U80), and the CW22/CW23 branch families.
    # 0xAx  memory, overflow from 0x2x: save and restore the pointers, and
    #       store an immediate without going through A
    "LDSPL": 0xA0, "LDSPH": 0xA1, "STSPL": 0xA2, "STSPH": 0xA3,
    "STPCL": 0xA4, "STPCH": 0xA5, "MVI": 0xA6, "MVIS": 0xA7,
    #       I/O, overflow from 0x5x: OUT an ALU result without storing it
    "OUTADD": 0xA8, "OUTSUB": 0xA9, "OUTBSUB": 0xAA,
    "OUTAND": 0xAB, "OUTOR": 0xAC, "OUTXOR": 0xAD,
    # 0xBx  moves, overflow from 0x8x: B and C to and from the pointers
    "MOVBSPL": 0xB0, "MOVBSPH": 0xB1, "MOVCSPL": 0xB2, "MOVCSPH": 0xB3,
    "MOVSPLB": 0xB4, "MOVSPHB": 0xB5, "MOVSPLC": 0xB6, "MOVSPHC": 0xB7,
    "MOVBPCL": 0xB8, "MOVBPCH": 0xB9, "MOVCPCL": 0xBA, "MOVCPCH": 0xBB,
    # 0xC0-0xD2  ALU with an IMMEDIATE operand. The biggest real win here:
    #       LDBI n; ADD is 3 bytes and 2 instructions, ADI n is 2 and 1, and
    #       CPI n + JNC is compare-against-a-constant-and-branch in four
    #       bytes -- the shape every loop bound and every status poll wants.
    "ADI": 0xC0, "ADI_B": 0xC1, "ADI_C": 0xC2,
    "SUI": 0xC3, "SUI_B": 0xC4, "SUI_C": 0xC5,
    "BSUI": 0xC6, "BSUI_B": 0xC7, "BSUI_C": 0xC8,
    "ANI": 0xC9, "ANI_B": 0xCA, "ANI_C": 0xCB,
    "ORI": 0xCC, "ORI_B": 0xCD, "ORI_C": 0xCE,
    "XRI": 0xCF, "XRI_B": 0xD0, "XRI_C": 0xD1,
    "CPI": 0xD2,
    # 0xD3-0xDF  ALU result into B or C instead of A. Writing B makes B an
    #       accumulator, since dst=REG_B refills TMP_B through the shadow
    #       latch; writing C computes without destroying either operand,
    #       because C has no shadow.
    "ADD_B": 0xD3, "ADD_C": 0xD4, "SUB_B": 0xD5, "SUB_C": 0xD6,
    "BSUB_B": 0xD7, "BSUB_C": 0xD8, "AND_B": 0xD9, "AND_C": 0xDA,
    "OR_B": 0xDB, "OR_C": 0xDC, "XOR_B": 0xDD, "XOR_C": 0xDE,
    "CPX": 0xDF,
    # 0xEx  the ALU result straight to memory, absolute and SP-relative
    "STADD": 0xE0, "STSUB": 0xE1, "STBSUB": 0xE2,
    "STAND": 0xE3, "STOR": 0xE4, "STXOR": 0xE5,
    "STADDS": 0xE6, "STSUBS": 0xE7, "STBSUBS": 0xE8,
    "STANDS": 0xE9, "STORS": 0xEA, "STXORS": 0xEB,
}

# CLR and SET are excluded from every immediate and every compute-and-store
# family: neither reads an operand, so the byte would be fetched and thrown
# away. See _CUT.
_REAL_SA = ("ADD", "SUB", "BSUB", "AND", "OR", "XOR")

# The three MAR prefixes and the byte length each costs. Every memory-
# touching family below is one of these plus a final row, which is why
# adding an addressing mode to an operation is one line and not three.
_PREFIXES = {"":  (3, _MARFILL),      # absolute, two operand bytes
             "X": (1, _BC_TO_MAR),    # indexed through B:C
             "S": (1, _SP_TO_MAR)}    # SP-relative


def _f_plus():
    """Build the 108 from the field tables rather than typing them out.

    108 hand-written rows is 108 chances to transpose a code, and the SA bug
    proved that a field which agrees with itself but not with the wiring is
    invisible until something computes with it. Everything this returns goes
    through check_word and check_table like any other row.
    """
    I = {}
    # ---- ALU with an immediate. Row 1 IS LDBI's row without END, so the
    # operand lands in TMP_B through the shadow latch (LE_TMP_B =
    # NOR(~{REG_B_LOAD}, CLK) follows the LOAD STROBE, not the opcode) and
    # row 2 computes on it. Clobbers B, exactly as LDBI n; ADD already does.
    for op, sa in zip(("ADI", "SUI", "BSUI", "ANI", "ORI", "XRI"), _REAL_SA):
        for suffix, dst in (("", "REG_A"), ("_B", "REG_B"), ("_C", "REG_C")):
            I[op + suffix] = (2, [
                word(mux_pc=True, pc_up=True, src="ROM", dst="REG_B"),
                SETTLE,
                word(end=True, sa=sa, src="ALU", dst=dst)])
    I["CPI"] = (2, [word(mux_pc=True, pc_up=True, src="ROM", dst="REG_B"),
                    SETTLE,
                    word(end=True, sa="SUB", src="ALU", dst="NONE")])
    # ---- ALU result into B or C, and two more flag-only tests
    for op, sa in zip(("ADD", "SUB", "BSUB", "AND", "OR", "XOR"), _REAL_SA):
        for suffix, dst in (("_B", "REG_B"), ("_C", "REG_C")):
            I[op + suffix] = (1, [word(end=True, sa=sa, src="ALU", dst=dst)])
    I["BIT"] = (1, [word(end=True, sa="AND", src="ALU", dst="NONE")])
    I["CPX"] = (1, [word(end=True, sa="XOR", src="ALU", dst="NONE")])
    # ---- B and C to and from the pointer halves
    for r in ("B", "C"):
        for h in ("LO", "HI"):
            I[f"MOV{r}SP{h[0]}"] = (1, [word(end=True, src=f"SP_{h}",
                                             dst=f"REG_{r}")])
            I[f"MOVSP{h[0]}{r}"] = (1, [word(end=True, src=f"REG_{r}",
                                             dst=f"SP_{h}")])
            I[f"MOV{r}PC{h[0]}"] = (1, [word(end=True, src=f"PC_{h}",
                                             dst=f"REG_{r}")])
    # ---- OUT from any source
    for name, src in (("OUTB", "REG_B"), ("OUTC", "REG_C"),
                      ("OUTSPL", "SP_LO"), ("OUTSPH", "SP_HI"),
                      ("OUTPCL", "PC_LO"), ("OUTPCH", "PC_HI")):
        I[name] = (1, [word(end=True, misc="REG_OUT_LOAD", src=src)])
    I["OUTI"] = (2, [word(mux_pc=True, pc_up=True, end=True,
                          misc="REG_OUT_LOAD", src="ROM")])
    for name, sa in zip(("OUTADD", "OUTSUB", "OUTBSUB", "OUTAND", "OUTOR",
                         "OUTXOR"), _REAL_SA):
        I[name] = (1, [word(end=True, misc="REG_OUT_LOAD", sa=sa, src="ALU")])
    # ---- the three addressing modes, x the operations that lacked one
    for p, (nbytes, pre) in _PREFIXES.items():
        I["OUTM" + p] = (nbytes, list(pre) + [
            word(end=True, misc="REG_OUT_LOAD", src="RAM")])
        # STORE AN IMMEDIATE -- and it costs one more T-state than it looks
        # like it should, for a reason worth stating.
        #
        # There is ONE address bus. The immediate is fetched at the PC and
        # written at MAR, and CW14 cannot point M at both in the same state.
        # So: fetch with the mux on the PC and NO destination, which parks the
        # byte in MDR for free (LE_MDR follows every memory read), then replay
        # it out of MDR with the mux back on MAR.
        #
        # And a SETTLE between them, 2026-09-05, found on silicon by
        # PROG_test5. CW14 comes straight off the ROM and flips M to MAR
        # ~30ns before the source decode retires ~{ROM_OUT}; in that window
        # FETCH_RAM = NOR(~{ROM_OUT}, ~{RAM_EN}) fires, the RAM drives the
        # cell's OLD byte onto MDR, and U18 is still transparent (LE_MDR
        # closes on READS_IDLE, three gates after the decode). The park shut
        # on a fight: MVI 0x9E read back 0x90/0x9F. A src=NONE row with the
        # mux STILL on the PC lets READ drop with M in ROM, so nothing can
        # turn on and the latch closes on a bus U19 released. Only then does
        # M flip. PROG_isa never saw it: PLANT rewrites the same byte.
        #
        # AND THE PC STEPS IN THE SETTLE, NOT IN THE PARK. First cut of the
        # settle (2026-09-05, burned, U9 0xC52B / U15 0xAE3F) left pc_up on
        # the park row: PC stepped at the boundary, the ROM's address moved
        # at once, and ~150ns later the ROM was putting the NEXT byte on U19
        # while U18 was still transparent. test5 slots 2/3 read 0x00/0xFF.
        # A ROM park is only safe while the ROM's ADDRESS stays put, so the
        # park reads without stepping and the settle steps: the PC moves at
        # the END of the settle, after U18 has shut on the immediate.
        I["MVI" + p] = (nbytes + 1, list(pre) + [
            word(mux_pc=True, src="ROM"),
            word(mux_pc=True, pc_up=True),
            word(end=True, misc="MDR_OUT", dst="RAM")])
        for name, sa in zip(("STADD", "STSUB", "STBSUB", "STAND", "STOR",
                             "STXOR"), _REAL_SA):
            I[name + p] = (nbytes, list(pre) + [
                word(end=True, sa=sa, src="ALU", dst="RAM")])
    # ---- save and restore the pointers, absolutely
    for h in ("LO", "HI"):
        I[f"LDSP{h[0]}"] = (3, _MARFILL + [word(end=True, src="RAM",
                                                dst=f"SP_{h}")])
        I[f"STSP{h[0]}"] = (3, _MARFILL + [word(end=True, src=f"SP_{h}",
                                                dst="RAM")])
        I[f"STPC{h[0]}"] = (3, _MARFILL + [word(end=True, src=f"PC_{h}",
                                                dst="RAM")])
        I[f"LXI{h[0]}"] = (2, [word(mux_pc=True, pc_up=True, end=True,
                                    src="ROM", dst=f"SP_{h}")])
    # ---- SP-relative for B and C
    for r in ("B", "C"):
        I[f"LD{r}S"] = (1, _SP_TO_MAR + [word(end=True, src="RAM",
                                              dst=f"REG_{r}")])
        I[f"ST{r}S"] = (1, _SP_TO_MAR + [word(end=True, src=f"REG_{r}",
                                              dst="RAM")])
    # ---- conditional branch to B:C
    for name, flag in (("JZX", "Z"), ("JCX", "C")):
        I[name] = (1, _BC_TO_MAR + [word(end=True, misc="COND",
                                         cond=(flag, 1))])
    # ---- push and pop the pointers
    for h in ("LO", "HI"):
        I[f"PUSHSP{h[0]}"] = (1, _PUSH(f"SP_{h}"))
        I[f"POPSP{h[0]}"] = (1, _POP(f"SP_{h}"))
        I[f"PUSHPC{h[0]}"] = (1, _PUSH(f"PC_{h}"))
    # ---- MEMORY-INDIRECT, the third addressing mode. RET's shape,
    # generalised.
    #
    # src=RAM CANNOT write MAR -- the address feeds back into the read while
    # the '373 is transparent -- so the pointer's LO byte is parked in C, MAR
    # is re-pointed at the pointer's HI byte, that byte is parked in MDR and
    # REPLAYED IMMEDIATELY (MDR holds for exactly one state), and only then
    # is MAR complete.
    #
    # THE ASSEMBLER EMITS THE ADDRESS TWICE, as addr then addr+1. MAR loads
    # only from W and has no increment, so the pointer's second half must be
    # addressed explicitly. That is the price of the mode and why these cost
    # five bytes.
    #
    # Clobbers C. B SURVIVES -- which is what makes LDAM better than
    # LDC addr; LDB addr+1; LDAX: five bytes against seven, and one fewer
    # register destroyed.
    def _indirect(final):
        return (_MARFILL + [word(src="RAM", dst="REG_C")]
                + _MARFILL
                + [word(src="RAM"),
                   word(misc="MDR_OUT", dst="MAR_HI"),
                   word(src="REG_C", dst="MAR_LO")]
                + final)
    I["LDAM"] = (5, _indirect([word(end=True, src="RAM", dst="REG_A")]))
    I["LDBM"] = (5, _indirect([word(end=True, src="RAM", dst="REG_B")]))
    I["STAM"] = (5, _indirect([word(end=True, src="REG_A", dst="RAM")]))
    I["JMPM"] = (5, _indirect([word(end=True, misc="PC_LOAD")]))
    I["JZM"] = (5, _indirect([word(end=True, misc="COND", cond=("Z", 1))]))
    I["JCM"] = (5, _indirect([word(end=True, misc="COND", cond=("C", 1))]))
    return I


_F_PLUS = _f_plus()

# The two tables must name the SAME set. A row with no opcode is unreachable;
# an opcode with no row safe-fills to a silent END. Both are bugs a bare
# update() would hide.
if set(_F_PLUS) != set(_OPCODES_F_PLUS):
    raise BuildError(
        f"phase F+ tables disagree -- rows without opcodes: "
        f"{sorted(set(_F_PLUS) - set(_OPCODES_F_PLUS))}; opcodes without "
        f"rows: {sorted(set(_OPCODES_F_PLUS) - set(_F_PLUS))}")
_collide = set(_OPCODES_F_PLUS.values()) & set(OPCODES.values())
if _collide:
    raise BuildError(f"phase F+ opcode collision: "
                     f"{sorted(hex(o) for o in _collide)}")
OPCODES.update(_OPCODES_F_PLUS)
INSTRUCTIONS.update(_F_PLUS)


# ==========================================================================
# INTERRUPTS -- 2026-09-25, Rico. .git/sdd/PROPOSAL_INT.md, as ruled:
# all six in 0x9x, K = 0x90, vector K:K = 0x9090, PUSHF/POPF in.
#
# 8080-style injection. At an instruction boundary (END, or HALT) with IE
# set and ~{IRQ} pending, the hardware holds the ROM/RAM buffers off for
# the next T0, drives K onto MDR from a '244, and inhibits PC_UP. The FETCH
# row runs unchanged -- IR latches K -- so the opcode below is never read
# from memory, and the PC still holds the address of the instruction that
# was NOT fetched. Everything after T0 is ordinary microcode.
#
# Decoder-inert until the hardware lands: no row of any other opcode names
# KONST, FLAGS, IE_SET or IE_CLR (test_interrupts pins every old row).
# ==========================================================================
KONST = 0x90                    # the '244's strapping: opcode AND vector byte
INT_VECTOR = (KONST << 8) | KONST   # 0x9090, in RAM: the vector is SOFT --
                                    # whoever EIs plants JMP handler here

_OPCODES_INT = {"INT": KONST, "IRET": 0x91, "EI": 0x92, "DI": 0x93,
                "PUSHF": 0x94, "POPF": 0x95}

# INT's first push is CALL's, with IE_CLR riding on the SP_DOWN row, whose
# DST field is otherwise empty. The microcode clears IE, so the accept
# logic does not have to: IE is 0 six states before INT's END, which is the
# first boundary at which a second accept could happen.
_INT_PUSH_HI = _PUSH_BYTE("PC_HI")
_INT_PUSH_HI = _INT_PUSH_HI[:-1] + [word(misc="SP_DOWN", dst="IE_CLR")]

_INT = {
    # 11 rows, 12 T. No pc_up anywhere: the PC already points at the
    # unfetched instruction, because the injected T0 did not count.
    "INT": (1, _INT_PUSH_HI + _PUSH_BYTE("PC_LO") + [
        word(src="KONST", dst="MAR_LO"),
        word(src="KONST", dst="MAR_HI"),
        word(end=True, misc="PC_LOAD"),
    ]),

    # IRET is NOT "RET plus one row", which is what the proposal said.
    # RET parks the return address's LO byte in C, and C belongs to the
    # interrupted program -- an IRET built that way breaks R3 on every
    # interrupt that lands while C is live. IRET parks LO in the PC
    # instead: the PC is about to be overwritten, so it is the one 16-bit
    # holder in the machine that is free here. 13 rows, 14 T.
    "IRET": (1, [
        word(misc="SP_UP"),
        word(src="SP_LO", dst="MAR_LO"),
        word(src="SP_HI", dst="MAR_HI"),
        word(src="RAM"),                        # return LO parked in MDR
        word(misc="MDR_OUT", dst="MAR_LO"),     # replayed immediately
        word(misc="PC_LOAD"),                   # PC = {SP_HI, LO}: scratch
        word(misc="SP_UP"),
        word(src="SP_LO", dst="MAR_LO"),
        word(src="SP_HI", dst="MAR_HI"),
        word(src="RAM"),                        # return HI parked in MDR
        word(misc="MDR_OUT", dst="MAR_HI"),     # replayed immediately
        word(src="PC_LO", dst="MAR_LO"),        # LO back out of the PC
        # IE_SET rides on the load: re-enable and return are one state, so
        # no 8080-style "EI takes effect after the next instruction" rule
        # is needed. No trailing pc_up -- INT has no operand bytes.
        word(end=True, misc="PC_LOAD", dst="IE_SET"),
    ]),

    "EI": (1, [word(end=True, dst="IE_SET")]),
    "DI": (1, [word(end=True, dst="IE_CLR")]),

    "PUSHF": (1, _PUSH("FLAGS")),
    # U49 clocks on ~{CLK}, MID T-state, not at the end (P_POPF). The
    # first RAM row loads nothing and lets the byte settle onto W for a
    # whole state; the second loads FLAGS from it. One T-state, bought
    # instead of a timing argument on breadboard bus capacitance.
    "POPF": (1, [word(misc="SP_UP")] + _SP_TO_MAR + [
        word(src="RAM"),
        word(end=True, src="RAM", dst="FLAGS"),
    ]),
}

if set(_INT) != set(_OPCODES_INT):
    raise BuildError("interrupt tables disagree")
_collide = set(_OPCODES_INT.values()) & set(OPCODES.values())
if _collide:
    raise BuildError(f"interrupt opcode collision: "
                     f"{sorted(hex(o) for o in _collide)}")
OPCODES.update(_OPCODES_INT)
INSTRUCTIONS.update(_INT)

# ==========================================================================
# CARRY INTO THE ALU -- 2026-10-06, Rico. PHASE_F 3.3, built as U76 (a '157
# on the ALU board; PHASE_F called it U80 before the INT block took that
# number). S <- CW16, I0a <- FLAG_C, I1a <- NAND(SA1, SA0), Za -> U38.15.
#
# CN is a true carry on ADD and a not-borrow on SUB, so both want FLAG_C
# straight: ADC = A + B + C, SBB = A - B - (1 - C). The immediate forms are
# ADI/SUI with CW16 cleared on the ALU row only -- the operand fetch is
# src=ROM, and U48 holds the flags unless the ALU is the source, so the
# carry they read is the one the previous instruction left.
# ==========================================================================
_OPCODES_CARRY = {"ADC": 0x96, "SBB": 0x97, "ACI": 0x98, "SBI": 0x99}

_CARRY = {
    "ADC": (1, [word(end=True, sa="ADD", src="ALU", dst="REG_A",
                     cin_from_flag_c=True)]),
    "SBB": (1, [word(end=True, sa="SUB", src="ALU", dst="REG_A",
                     cin_from_flag_c=True)]),
    "ACI": (2, INSTRUCTIONS["ADI"][1][:-1] + [
        INSTRUCTIONS["ADI"][1][-1] & ~CIN_SEL_N]),
    "SBI": (2, INSTRUCTIONS["SUI"][1][:-1] + [
        INSTRUCTIONS["SUI"][1][-1] & ~CIN_SEL_N]),
}

if set(_CARRY) != set(_OPCODES_CARRY):
    raise BuildError("carry tables disagree")
_collide = set(_OPCODES_CARRY.values()) & set(OPCODES.values())
if _collide:
    raise BuildError(f"carry opcode collision: "
                     f"{sorted(hex(o) for o in _collide)}")
OPCODES.update(_OPCODES_CARRY)
INSTRUCTIONS.update(_CARRY)

# Assemblers refuse these by name. INT exists only as an injected opcode:
# fetched from memory, the FETCH row would count the PC and INT would push
# a return address one byte past the truth.
NOT_ASSEMBLABLE = frozenset({"INT"})


def _fields(w):
    """(misc, src, dst) as FULL codes, bank bits folded in.

    This MUST fold the bank bits, and the reason is concrete: bank-1 code 10
    (`PC_LO`) has low bits `010`, the same three bits `RAM` uses in bank 0.
    The bank-blind version of this function raised "src=RAM dst=RAM" on
    CALL's push row -- a false positive -- and would just as happily have
    MISSED a genuine bank-1 bus fight. Every rule below compares full codes.
    """
    misc = ((w >> 6) & 7) | (0 if w & MISC_BANK_N else 8)
    src = ((w >> 3) & 7) | (0 if w & SRC_BANK_N else 8)
    dst = (w & 7) | (0 if w & DST_BANK_N else 8)
    return misc, src, dst


def check_word(addr, w):
    """Per-word legality. addr names the row in errors."""
    misc, src, dst = _fields(w)
    where = f"row {addr:#05x} word {w:#06x}"
    # src device == dst device (RAM corrupts; register case is the warning)
    if src == SRC["RAM"] and dst == DST["RAM"]:
        raise BuildError(f"{where}: src=RAM dst=RAM")
    for r in ("REG_A", "REG_B", "REG_C"):
        if src == SRC[r] and dst == DST[r]:
            print(f"WARNING {where}: src=dst={r} (probable MOV typo)")
    # /MDR_OUT replay + ANY source, in EITHER BANK, = two MDR-bus drivers.
    # MISC is an independent field, so this is the one collision the
    # hardware cannot prevent: every SRC-driven buffer is gated by U28 or
    # U70, which are one-hot and mutually exclusive by construction, but
    # U18's ~{MDR_OUT} comes from U29 and can be asserted alongside any of
    # them. Bank 1 widened the set this has to cover from 7 sources to 11.
    if misc == MISC["MDR_OUT"] and src != SRC["NONE"]:
        raise BuildError(f"{where}: /MDR_OUT with src!=NONE (MDR-bus fight)")
    # A RAM READ CANNOT WRITE MAR IN THE SAME WORD. The RAM address IS MAR
    # (U54/U59 -> M), and MAR's '373s are TRANSPARENT while CLK is low -- so
    # src=RAM with dst=MAR_LO/MAR_HI closes a live combinational loop:
    # MAR -> M -> RAM -> MDR -> U25 -> W -> MAR. The address changes
    # underneath the read.
    #
    # Found the hard way on 2026-08-10: RET's first draft did exactly this to
    # get the return address's HI byte into MAR, and the gate model hung with
    # the PC at 0x8D00. Park the byte in MDR instead (src=RAM with NO dst --
    # MDR shadows it for free) and replay it with misc=MDR_OUT.
    #
    # ROM reads are NOT affected: their address comes from the PC through
    # MUX_PC, not from MAR, which is why _MARFILL's ROM->MAR_LO/MAR_HI rows
    # are safe and always have been.
    if src == SRC["RAM"] and dst in (DST["MAR_LO"], DST["MAR_HI"]):
        raise BuildError(f"{where}: src=RAM writing MAR (the address feeds "
                         f"back into the read while the '373 is transparent)")
    # SP cannot count and be read in the same word: the '169s commit on the
    # CLK edge that ENDS the T-state, so the byte on MDR during that state
    # is the PRE-count value while the row reads as though it were the
    # post-count one. Ambiguous by construction -- refuse to encode it.
    if misc in (MISC["SP_UP"], MISC["SP_DOWN"]) and src in (SRC["SP_LO"], SRC["SP_HI"]):
        raise BuildError(f"{where}: SP counted and read in the same word")
    # THE ADDRESS BUS CARRIES ONE ADDRESS. CW14 (PC_MAR_MUX) points M at the
    # PC or at MAR, and a row cannot have it both ways:
    #
    #   src=ROM  needs the PC on M    (mux_pc=1)
    #   src=RAM  needs MAR on M       (mux_pc=0)
    #   dst=RAM  needs MAR on M       (mux_pc=0)  -- the write address is MAR
    #
    # So src=ROM with dst=RAM is UNSATISFIABLE, and it does not fail loudly:
    # the mux stays on the PC and the byte is written to the PC's own address,
    # which is ROM, so the store simply evaporates.
    #
    # PAID FOR ON 2026-08-27. MVI/MVIX/MVIS were encoded exactly that way. On
    # the bench the symptom was a program whose answer CHANGED ON EVERY RESET
    # -- its loop counter was initialised with MVI, the store went nowhere,
    # and the count came from uninitialised RAM. Nothing in check_word looked
    # at CW14 at all, so 174 instructions passed the police with three of them
    # unable to work. The cure is the MDR park: fetch with the mux on the PC
    # and NO destination, then replay out of MDR with the mux on MAR.
    if src == SRC["ROM"] and dst == DST["RAM"]:
        raise BuildError(f"{where}: src=ROM with dst=RAM -- one address bus, "
                         f"and the fetch and the store want different halves "
                         f"of it. Park the byte in MDR and replay it")
    if (w & MUX_PC) and (src == SRC["RAM"] or dst == DST["RAM"]):
        raise BuildError(f"{where}: RAM accessed with mux_pc set -- M carries "
                         f"the PC, not MAR, so the access lands at the wrong "
                         f"address")
    if src == SRC["ROM"] and not (w & MUX_PC):
        raise BuildError(f"{where}: src=ROM without mux_pc -- M carries MAR, "
                         f"so the fetch reads the wrong address")
    # THE FLAG CARRY IS FOR ARITHMETIC ON THE ALU. CW16 low hands U38.15
    # FLAG_C through U76; the '382 ignores CN on its logic codes, and with
    # no ALU source nothing computes. Either row encodes cleanly, burns,
    # and silently does what the same row without the bit does.
    if not (w & CIN_SEL_N):
        sa_code = _sa_bits((w >> 9) & 7)
        if src != SRC["ALU"] or sa_code not in (SA["ADD"], SA["SUB"],
                                                SA["BSUB"]):
            raise BuildError(f"{where}: flag carry (CW16 low) needs src=ALU "
                             f"and ADD/SUB/BSUB -- CN means nothing else")
    # PC_UP + PC_LOAD same word: defined-but-fragile on '193 internals
    if (w & PC_UP) and misc == MISC["PC_LOAD"]:
        raise BuildError(f"{where}: PC_UP with /PC_LOAD")
    # IR changes only at fetch
    if dst == DST["IR"] and (addr & 0xF) != 0:
        raise BuildError(f"{where}: IR_LOAD outside T0")
    # T0 row of every opcode is the universal fetch
    if (addr & 0xF) == 0 and w != FETCH:
        raise BuildError(f"{where}: T0 row is not the fetch word {FETCH:#06x}")


def check_table(words):
    """Whole-image legality: per-word checks + per-opcode block shape."""
    assert len(words) == 4096
    for a, w in enumerate(words):
        check_word(a, w)
    for op in range(256):
        block = words[op * 16:op * 16 + 16]
        # an instruction must END (or HALT-freeze) before running off its
        # last defined state into safe-fill. Safe-fill is itself END, so
        # scan T1..last-non-fill row: that word must carry END or HALT.
        states = [w for w in block[1:] if w != FILL]
        if states and not (states[-1] & (END | HALT_BIT)):
            raise BuildError(f"opcode {op:#04x}: last state "
                             f"{states[-1]:#06x} has no END/HALT")
        _check_mar_before_ram(op, states)
        _check_mdr_replay_is_immediate(op, states)


def _check_mdr_replay_is_immediate(op, states):
    """misc=MDR_OUT must be the state IMMEDIATELY after the read that parked
    the byte.

    MDR is a genuinely useful second scratch -- U18 shadows every W transfer
    for free -- but the park is only good for ONE state. LE_MDR =
    NAND(~{RAM_LOAD}, READS_IDLE) falls as ~{RAM_OUT} deasserts at the
    T-state boundary, and if another source is turning ON across that same
    boundary the latch can capture THAT byte instead. It is a race, not a
    rule, so it cannot be reasoned about from the gate equations alone.

    Paid for on 2026-08-10: RET's second draft parked the return address's HI
    byte in MDR, moved the LO byte from C to MAR_LO, and only THEN replayed.
    U18 latched C, MAR_HI got 0x0C instead of 0x00, and RET loaded the PC
    with 0x0C0C. Every reading of the schematic said the park was safe; the
    gate model disagreed, which is the whole reason the FPGA is the primary
    instrument now.
    """
    for t, w in enumerate(states, start=1):
        misc, src, _ = _fields(w)
        if misc != MISC["MDR_OUT"]:
            continue
        if t < 2:
            raise BuildError(f"opcode {op:#04x} T{t}: MDR_OUT with no prior "
                             f"state to have parked a byte")
        prev_misc, prev_src, prev_dst = _fields(states[t - 2])
        # One src=NONE settle between the park and the replay is allowed,
        # and for a ROM-side park it is REQUIRED (see the MVI family): it
        # drives nothing and loads nothing, so the latch has nothing new to
        # capture, and it keeps the mux where the park left it so no
        # address-keyed enable can fire. 2026-09-05.
        if (prev_src == SRC["NONE"] and prev_dst == DST["NONE"]
                and prev_misc == MISC["NONE"] and t >= 3
                and (states[t - 2] & MUX_PC) == (states[t - 3] & MUX_PC)):
            prev_misc, prev_src, prev_dst = _fields(states[t - 3])
        if prev_src not in (SRC["ROM"], SRC["RAM"]):
            raise BuildError(
                f"opcode {op:#04x} T{t}: MDR_OUT replays a byte that was not "
                f"parked by the preceding state (T{t-1} has src={prev_src}, "
                f"needs ROM or RAM, or one src=NONE settle after one) -- MDR "
                f"holds only until another source turns on, see "
                f"_check_mdr_replay_is_immediate")


def _check_mar_before_ram(op, states):
    """A RAM access must be preceded, in the SAME instruction, by BOTH MAR
    halves being loaded.

    The hardware already prevents the dangerous case -- ~{RAM_WRITE_EN} =
    NAND(~{CLK}, WRITE_DIR) and WRITE_DIR = NOT(~{RAM_LOAD}), so no write
    strobe exists on a row whose DST is not RAM, and the half-updated MAR
    that occurs on EVERY memory instruction (_MARFILL loads LO at T1, HI at
    T2) can never fire one.

    What the hardware cannot prevent is MICROCODE authored in the wrong
    order: a row with DST=RAM before both halves are set writes to a real
    address, in the wrong place, silently. That is exactly the shape a PUSH
    sequence typed one T-state out of order would take, and the stack made
    it worth policing rather than leaving incidental.
    """
    lo = hi = False
    for t, w in enumerate(states, start=1):
        _, src, dst = _fields(w)
        if dst == DST["MAR_LO"]: lo = True
        if dst == DST["MAR_HI"]: hi = True
        if (src == SRC["RAM"] or dst == DST["RAM"]) and not (lo and hi):
            raise BuildError(
                f"opcode {op:#04x} T{t}: RAM accessed with MAR incomplete "
                f"(MAR_LO={'set' if lo else 'UNSET'}, "
                f"MAR_HI={'set' if hi else 'UNSET'})")


# Instructions whose PC_UP count is deliberately NOT their byte length,
# each with the reason. An exemption has to be named here to be silent --
# the check still polices everything else.
_PC_UP_EXEMPT = {
    "RET": "1 byte, 3 PC_UPs: the fetch plus two bare steps over CALL's "
           "operand bytes. CALL pushes the address of its OPERANDS (MAR is "
           "the only 16-bit holder, so the push must finish before the "
           "target fetch reuses it), and stepping over them is the price.",
}


def _check_lengths():
    for name, (nbytes, states) in INSTRUCTIONS.items():
        ups = sum(1 for w in [FETCH] + states if w & PC_UP)
        if ups != nbytes and name not in _PC_UP_EXEMPT:
            print(f"WARNING {name}: PC_UP count {ups} != byte length {nbytes}")


# ---- images -------------------------------------------------------------
def build_real():
    words = [FILL] * 4096
    for op in range(256):
        words[op * 16] = FETCH
    for name, (_, states) in INSTRUCTIONS.items():
        base = OPCODES[name] * 16
        for t, w in enumerate(states, start=1):
            words[base + t] = w
    _check_lengths()
    check_table(words)
    return words


def build_diag():
    return [a | ((~(a >> 8) & 0xF) << 12) for a in range(4096)]


def diag_third(words):
    """U23's diagnostic byte.

    `U9_diag` carries a[7:0] and `U15_diag` carries a[11:8] plus its inverse.
    The third ROM has NO address bits left, so a constant fill would leave
    eight data lines that no sweep exercises -- the same problem CW12-15 had,
    eight times over.

        U23_diag[a] = ~(((a >> 4) & 0xFF) ^ (a & 0x0F))

    A4-A11 reach bits 0-7 through `a >> 4`; A0-A3 reach bits 0-3 through
    `a & 0xF`. Every one of the twelve address lines affects the byte, every
    one of the eight data lines takes both values, and the pattern is distinct
    from both other chips so a swapped-ROM fault cannot alias.

    REJECTED EARLIER RULE, recorded so it is not re-proposed: `~((a >> 4) &
    0xFF)` alone. Address = {IR[7:0], T[3:0]}, so `a >> 4` IS `IR` exactly and
    the byte never varies with T -- it cannot detect a swap among MCA0-MCA3,
    which is precisely the fault class a diag image exists to catch.
    """
    return bytes((~(((a >> 4) & 0xFF) ^ (a & 0x0F))) & 0xFF
                 for a in range(len(words)))


def crc16(data):
    """CRC-16/CCITT-FALSE: poly 0x1021, init 0xFFFF. Mirrors src/crc16.c."""
    crc = 0xFFFF
    for b in data:
        crc ^= b << 8
        for _ in range(8):
            crc = ((crc << 1) ^ 0x1021 if crc & 0x8000 else crc << 1) & 0xFFFF
    return crc


# U23's byte, CW16-23 -- the third EEPROM, schematic 2026-08-10.
#
# EVERY new field is polarised so 0xFF is TODAY'S MACHINE:
#
#   CW16 ~{CIN_SEL}    1 = the existing NOT(SA1 AND SA0) carry path
#   CW17 ~{SRC_BANK}   1 = SRC bank 0 (U28 enabled via E3, U70 dark via E1)
#   CW18 ~{DST_BANK}   1 = DST bank 0
#   CW19 ~{MISC_BANK}  1 = MISC bank 0        (unwired, in reserve)
#   CW20 ~{ADDR_SEL1}  1 = ADDR_SEL1 low, CW14 alone picks MAR/PC (unwired)
#   CW21 FLAG_SEL0  \
#   CW22 FLAG_SEL1   > don't-care unless MISC=COND is decoded  (unwired)
#   CW23 FLAG_POL   /
#
# So an ERASED AT28C64B is a valid U23 image, and that is not a coincidence
# -- it is the property the polarities were chosen for (same reasoning that
# made HALT=0xFF). Until the fields are actually encoded, THIRD = 0xFF is the
# correct image, not a placeholder: it reproduces the 16-bit machine exactly.
#
# The one row that will differ once FLAG_SEL/FLAG_POL are encoded is JNZ's
# MISC=COND T-state (FLAG_SEL=Z, FLAG_POL=1 -> 0xBF), matching today's
# COND_TAKEN = NOR(~{COND}, FLAG_Z). The COND hardware ('153 + '86) does not
# exist yet, so 0xFF is correct for it too right now.
THIRD_INERT = 0xFF


def third(words):
    """U23 = word[23:16] = CW16-23."""
    return bytes((w >> 16) & 0xFF if w > 0xFFFF else THIRD_INERT
                 for w in words)


def split(words):
    lo = bytes(w & 0xFF for w in words)      # U9  = CW0-7
    hi = bytes((w >> 8) & 0xFF for w in words)   # U15 = CW8-15
    return lo, hi


def _mirror(half):                            # A12 grounded: 2x the image
    return half + half


def emit_header(real, crcs, path):
    lines = [
        "/* GENERATED by microcode_gen.py — do not hand-edit.",
        "   Regenerate: python3 docs/notes/microcode_gen.py */",
        "#ifndef MICROCODE_EXPECT_H",
        "#define MICROCODE_EXPECT_H",
        "#ifdef __AVR__",
        "#include <avr/pgmspace.h>",
        "#else",
        "#define PROGMEM",
        "#endif",
        "#include <stdint.h>",
        "",
        "/* image-detect signatures: row 0 of each burn */",
        f"#define MC_REAL_ROW0 0x{real[0]:06X}UL",
        f"#define MC_DIAG_ROW0 0x{build_diag()[0]:04X}",
        "",
        "/* CRC-16/CCITT-FALSE over the 4096 addressable bytes per chip */",
    ]
    for name, val in crcs.items():
        lines.append(f"#define {name} 0x{val:04X}")
    lines += [
        "",
        "/* diag word is a pure function of its row (test spec, ROM images):",
        "   addr[11:0] in the data, INVERTED addr[11:8] in [15:12] */",
        "#define MC_DIAG_WORD(a) ((uint16_t)(((a) & 0x0FFF) | "
        "((uint16_t)(~((a) >> 8) & 0xF) << 12)))",
        "",
        "/* the shipped real image, row-addressable for bench diagnostics.",
        "   24 BITS since 2026-08-10 -- U23 carries CW16-23, so a uint16_t",
        "   here would silently truncate every bank bit. */",
        "static const uint32_t MC_REAL_WORDS[4096] PROGMEM = {",
    ]
    for i in range(0, 4096, 8):
        row = ", ".join(f"0x{w:06X}UL" for w in real[i:i + 8])
        lines.append(f"    {row},")
    # THE IMPLEMENTED OPCODE LIST. Cannot be inferred from the image: T0 is
    # the universal FETCH row for ALL 256 opcodes, and NOP's T1 is a bare END
    # identical to the FILL written at every unimplemented opcode. A rig that
    # guesses "is this opcode real?" from the words will walk all 256 and
    # compare 238 of them against fill. (Cost one Block 1 bench run to learn,
    # 2026-07-30.)
    ops = sorted(OPCODES.items(), key=lambda kv: kv[1])
    lines += [
        "};",
        "",
        "/* Every opcode the microcode actually implements, ascending. */",
        f"#define MC_OPCODE_COUNT {len(ops)}u",
        "static const uint8_t MC_OPCODES[MC_OPCODE_COUNT] PROGMEM = {",
        "    " + ", ".join(f"0x{v:02X}" for _n, v in ops) + ",",
        "};",
        "",
        "/* Opcodes whose last row carries HALT instead of END. END-segmented",
        "   capture cannot bracket these — the sequencer stops. */",
        "#define MC_HALT_OPCODE 0x%02Xu" % OPCODES["HALT"],
        "",
        "#endif", ""]
    with open(path, "w") as f:
        f.write("\n".join(lines))


def main():
    real, diag = build_real(), build_diag()
    os.makedirs(ROMS, exist_ok=True)
    crcs = {}
    for tag, words in (("REAL", real), ("DIAG", diag)):
        lo, hi = split(words)
        thd = third(words) if tag == "REAL" else diag_third(words)
        for chip, half in (("U9", lo), ("U15", hi), ("U23", thd)):
            fn = f"{chip}.bin" if tag == "REAL" else f"{chip}_diag.bin"
            with open(os.path.join(ROMS, fn), "wb") as f:
                f.write(_mirror(half))
            crcs[f"MC_CRC_{chip}_{tag}"] = crc16(half)
    emit_header(real, crcs, HDR)
    print(f"wrote 6x 8192B bins -> {ROMS}")
    print(f"wrote expect header -> {HDR}")
    print("burn order: DIAG set first (addr/split tests), REAL set second")
    print("  U9  = word[7:0]   = CW0-7   (low byte)")
    print("  U15 = word[15:8]  = CW8-15  (high byte)")
    print("  U23 = word[23:16] = CW16-23 (third ROM)")
    print("  ALL THREE need burning when an INSTRUCTION is added or changed:")
    print("  a new opcode writes rows in every byte of the word. U9/U15 stay")
    print("  untouched only for changes confined to CW16-23.")
    for name, val in crcs.items():
        print(f"  {name} = 0x{val:04X}")
    return 0


if __name__ == "__main__":
    sys.exit(main())
