robertrico/dino-homebrew/docs/notes/power_sheet_gen.py

#!/usr/bin/env python3
"""Draw the core's Power sheet: a 24-pin ATX header for the picoPSU, its
rails on the project's power nets, PS_ON# on a 2-pin header for the panel
switch.

    python3 docs/notes/power_sheet_gen.py --write     dino_v0_0_2/power.kicad_sch
                                                      + a sheet block on the root

Rico, 2026-09-12: power is off the shelf (picoPSU-160-XT or -120-WI-25,
both 24-pin ATX). The rails drawn are exactly the ones those deliver and
the core uses or publishes: +5V, +3.3V, +12V, -12V, GND. No -5V (no ATX
unit since 2003 has one), no regulator on the core. +5VSB and PWR_OK are
brought to no-connects: real pins, nothing consumes them.

The sheet is a one-shot scaffold. Once it exists KiCad owns it; rerunning
`--write` on a project that already has a power sheet changes nothing.

Symbol definitions are copied VERBATIM out of KiCad 10's own libraries, so
the embedded lib_symbols match what the editor would embed itself.
"""
import os
import re
import sys
import uuid as _uuid

HERE = os.path.dirname(os.path.abspath(__file__))
sys.path.insert(0, HERE)
from kicad_netlist import tokenize, parse, children, child  # noqa: E402
import footprint_gen as fg  # noqa: E402

SYM_DIR = "/Applications/KiCad/KiCad.app/Contents/SharedSupport/symbols"
PROJECT = "dino_v0_0_2"
ROOT_UUID = "e43166a5-d972-471d-b3cf-9f4f12c7f541"

ATX_REF = "J9"          # J1-J8 are reserved for the eight edge sockets
PSON_REF = "J10"
SHEET_NAME = "Power"
SHEET_FILE = "power.kicad_sch"
SHEET_AT = (182.88, 58.42)      # free cell on the root page, under Register Modules

# --- symbol geometry (lib units, Y up) ---------------------------------------
# ATX-24 pin connection points, read from Connector.kicad_sym. Stacked pins
# share a point, so one wire serves the whole rail.
ATX_PINS = {
    "+3.3V": (12.7, -2.54),
    "+5V": (12.7, 2.54),
    "+5VSB": (12.7, 0.0),
    "+12V": (12.7, 5.08),
    "PWR_OK": (12.7, 10.16),
    "-12V": (12.7, -10.16),
    "GND": (0.0, -15.24),
    "PS_ON#": (-12.7, 10.16),
}
ATX_AT = (101.6, 88.9)
RAIL_RUN = 12.7          # wire length from the header's right-hand pins

# --- s-expression text helpers ------------------------------------------------


def _uid():
    return str(_uuid.uuid4())


def raw_symbol(lib, name):
    """The `(symbol "<name>" ...)` block from KiCad's <lib>.kicad_sym, text
    verbatim, renamed to "<lib>:<name>" the way eeschema embeds it."""
    with open(os.path.join(SYM_DIR, lib + ".kicad_sym")) as f:
        src = f.read()
    head = f'(symbol "{name}"'
    start = src.index("\t" + head + "\n")
    depth, i, in_str = 0, start + 1, False
    while True:
        c = src[i]
        if in_str:
            if c == "\\":
                i += 1
            elif c == '"':
                in_str = False
        elif c == '"':
            in_str = True
        elif c == "(":
            depth += 1
        elif c == ")":
            depth -= 1
            if depth == 0:
                break
        i += 1
    block = src[start + 1:i + 1]
    return "\t" + block.replace(head, f'(symbol "{lib}:{name}"', 1) + "\n"


def _q(s):
    """Quote a string the way eeschema does. 2026-09-12: an unescaped `"`
    inside a Description made KiCad stop reading the sheet at that symbol,
    silently -- half the page vanished and no tool said a word."""
    return '"' + s.replace("\\", "\\\\").replace('"', '\\"') + '"'


def _prop(name, value, x, y, hide=False, extra=""):
    h = "\t\t\t(hide yes)\n" if hide else ""
    return (f'\t\t(property {_q(name)} {_q(value)}\n'
            f"\t\t\t(at {x:g} {y:g} 0)\n{h}"
            "\t\t\t(show_name no)\n\t\t\t(do_not_autoplace no)\n"
            "\t\t\t(effects\n\t\t\t\t(font\n\t\t\t\t\t(size 1.27 1.27)\n\t\t\t\t)\n"
            f"{extra}\t\t\t)\n\t\t)\n")


def symbol(lib_id, ref, value, x, y, pins, path, footprint="", rot=0,
           datasheet="", description="", mirror=None):
    hidden_ref = ref.startswith("#")
    pins_txt = "".join(f'\t\t(pin "{p}"\n\t\t\t(uuid "{_uid()}")\n\t\t)\n'
                       for p in pins)
    return (
        "\t(symbol\n"
        f'\t\t(lib_id "{lib_id}")\n'
        f"\t\t(at {x:g} {y:g} {rot})\n"
        + (f"\t\t(mirror {mirror})\n" if mirror else "")
        + "\t\t(unit 1)\n\t\t(body_style 1)\n\t\t(exclude_from_sim no)\n"
        "\t\t(in_bom yes)\n\t\t(on_board yes)\n\t\t(in_pos_files yes)\n"
        "\t\t(dnp no)\n\t\t(fields_autoplaced yes)\n"
        f'\t\t(uuid "{_uid()}")\n'
        + _prop("Reference", ref, x, y - 7.62, hide=hidden_ref)
        + _prop("Value", value, x, y - 5.08)
        + _prop("Footprint", footprint, x, y, hide=True)
        + _prop("Datasheet", datasheet, x, y, hide=True)
        + _prop("Description", description, x, y, hide=True)
        + pins_txt
        + "\t\t(instances\n"
        f'\t\t\t(project "{PROJECT}"\n'
        f'\t\t\t\t(path "{path}"\n'
        f'\t\t\t\t\t(reference "{ref}")\n\t\t\t\t\t(unit 1)\n'
        "\t\t\t\t)\n\t\t\t)\n\t\t)\n\t)\n")


def wire(x1, y1, x2, y2):
    return (f"\t(wire\n\t\t(pts\n\t\t\t(xy {x1:g} {y1:g}) (xy {x2:g} {y2:g})\n"
            "\t\t)\n\t\t(stroke\n\t\t\t(width 0)\n\t\t\t(type default)\n\t\t)\n"
            f'\t\t(uuid "{_uid()}")\n\t)\n')


def no_connect(x, y):
    return f'\t(no_connect\n\t\t(at {x:g} {y:g})\n\t\t(uuid "{_uid()}")\n\t)\n'


def text(s, x, y):
    # eeschema stores a newline as the two characters `\n`; quote first,
    # then break lines, or the backslash gets escaped too
    s = _q(s).replace("\n", "\\n")
    return (f'\t(text {s}\n\t\t(exclude_from_sim no)\n\t\t(at {x:g} {y:g} 0)\n'
            "\t\t(effects\n\t\t\t(font\n\t\t\t\t(size 1.27 1.27)\n\t\t\t)\n"
            f"\t\t\t(justify left bottom)\n\t\t)\n\t\t(uuid \"{_uid()}\")\n\t)\n")


def power_refs(src):
    return set(re.findall(r'"(#PWR0?\d+)"', src))


def _pin_xy(at, lib_xy):
    """Lib coordinates are Y-up; the sheet is Y-down."""
    return (at[0] + lib_xy[0], at[1] - lib_xy[1])


# --- the sheet ----------------------------------------------------------------
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
