robertrico/dino-homebrew/docs/images/MEMORY_MAPPED_I_O.jpeg

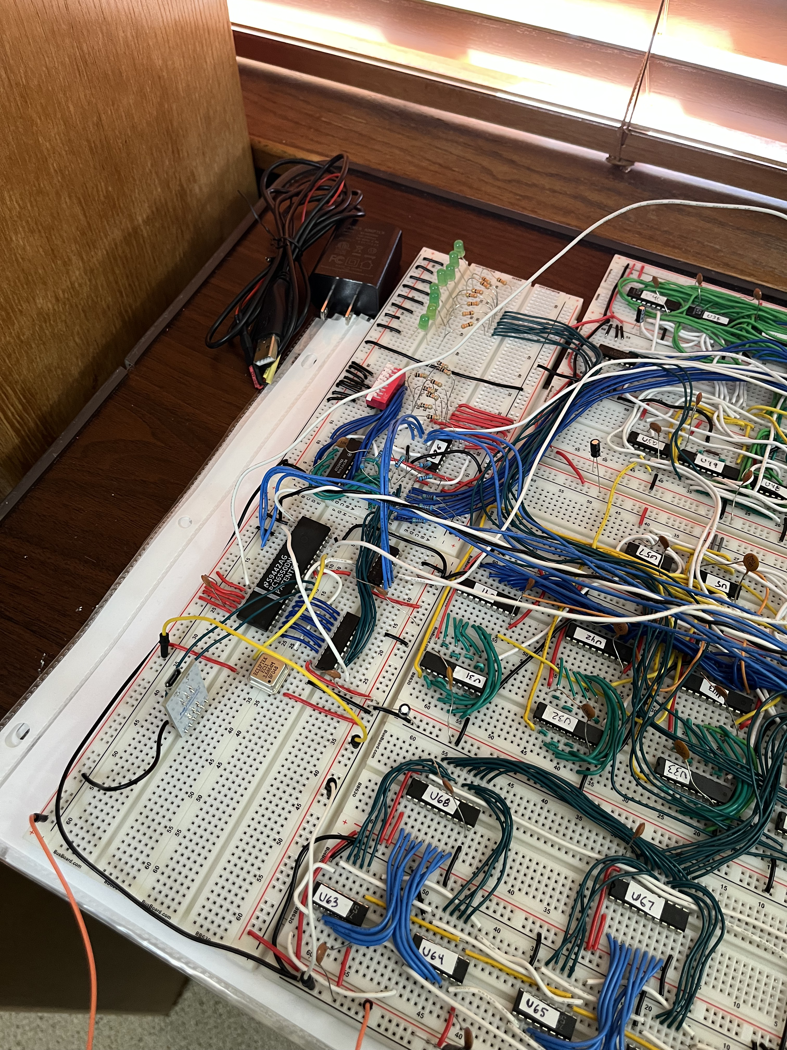
docs/images/MEMORY_MAPPED_I_O.jpeg
